ElRojo/button-box/3d files/lid_7mm_switches.stl

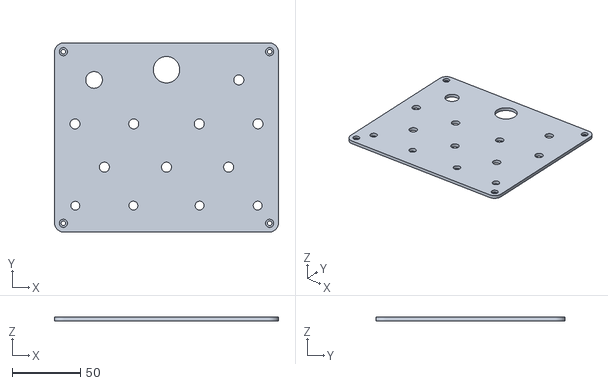
[picture p18: CAD file, 2024-11-30]
3d files/lid_7mm_switches.stl
164.4 x 139.0 x 2.75
